Josephrp/Meteor-On-Mesh/firmwares/mayhem-firmware/hardware/portapack_h4m/CPLD_Schematic.pdf

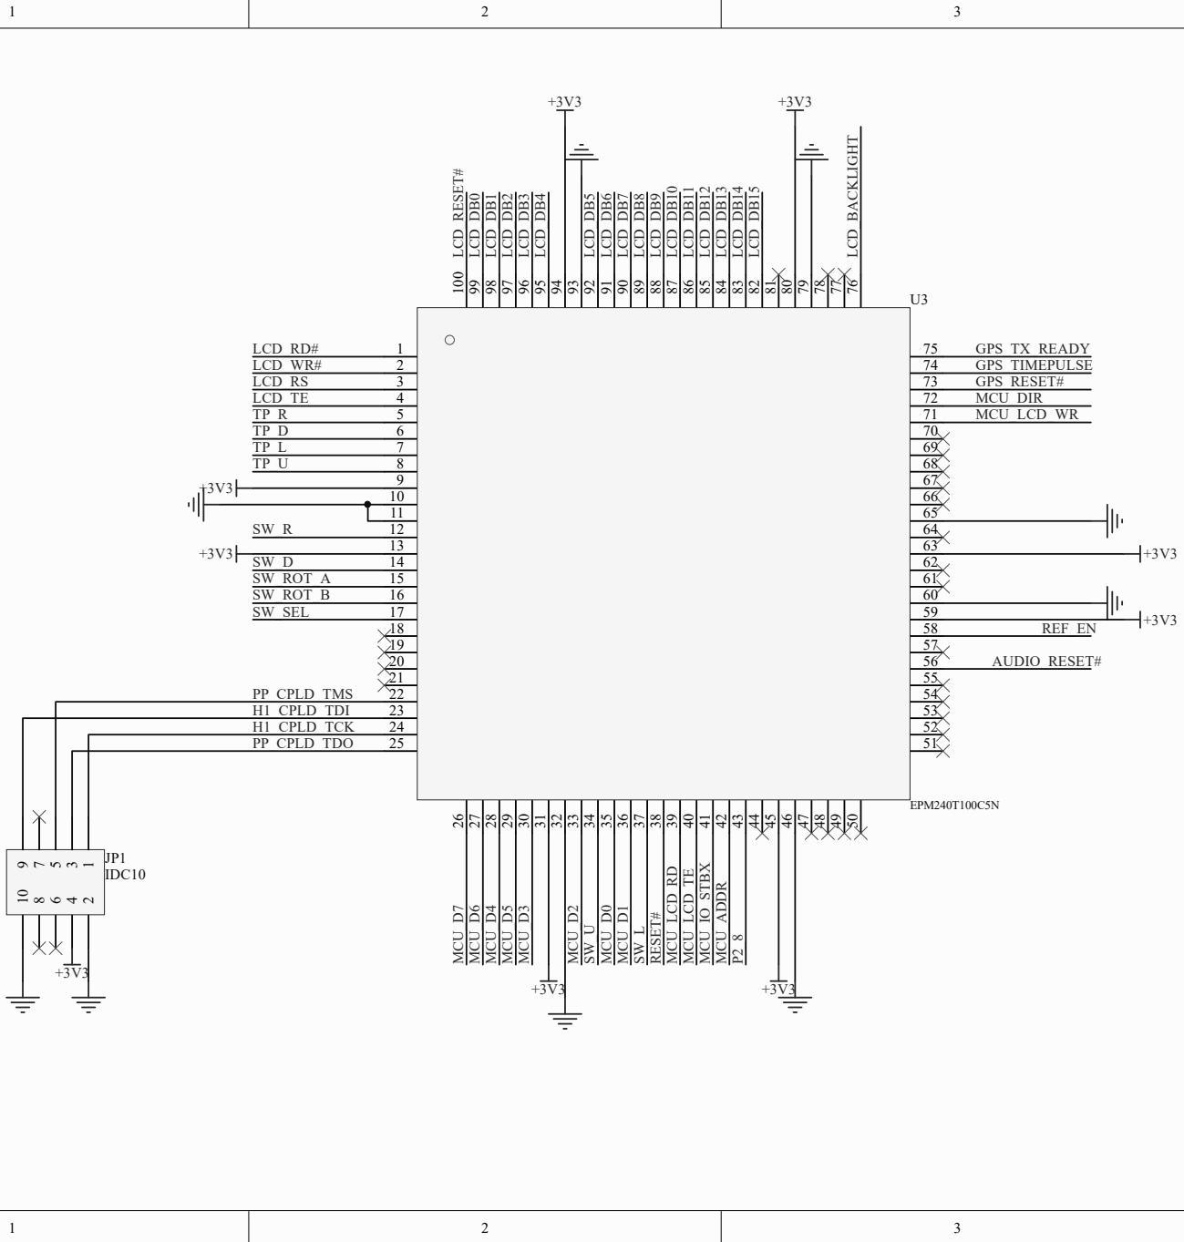
[picture p5: figure]
LCD_DB10; LCD_DB11; LCD_DB12; LCD_DB13; LCD_DB14; LCD_DB15; MCU_DIR MCU_LCD_WR; LCD_RESET#; LCD_BACKLIGHT; GPS_TX_READY GPS_TIMEPULSE; MCU_ADDR; PP_CPLD_TDO; MCU_D7; MCU_D6; MCU_D4; MCU_D5; MCU_D3; MCU_D2; MCU_D0; MCU_D1; RESET#; MCU_LCD_RD; MCU_LCD_TE; MCU_IO_STBX; H1_CPLD_TCK; SW_D SW_ROT_A SW_ROT_B SW_SEL; PP_CPLD_TMS H1_CPLD_TDI; GPS_RESET#; AUDIO_RESET#; REF_EN; LCD_TE; LCD_WR#; LCD_RD#; LCD_DB0; LCD_DB1; LCD_RS; LCD_DB2; LCD_DB3; LCD_DB4; LCD_DB5; LCD_DB6; LCD_DB7; LCD_DB8; LCD_DB9; EPM240T100C5N; JP1 IDC10

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
