Josephrp/Meteor-On-Mesh/firmwares/mayhem-firmware/docs/images/h2_cover.jpg

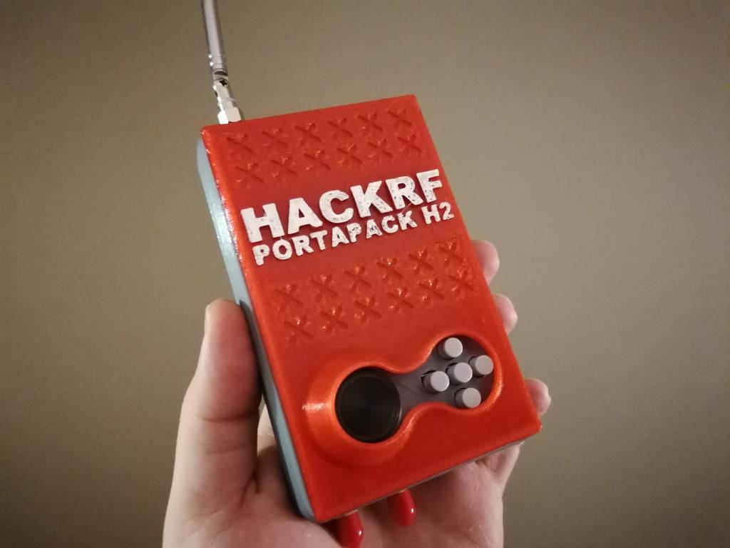
firmwares/mayhem-firmware/docs/images/h2_cover.jpg
