Josephrp/Meteor-On-Mesh/firmwares/mayhem-firmware/docs/images/h2_front.jpg

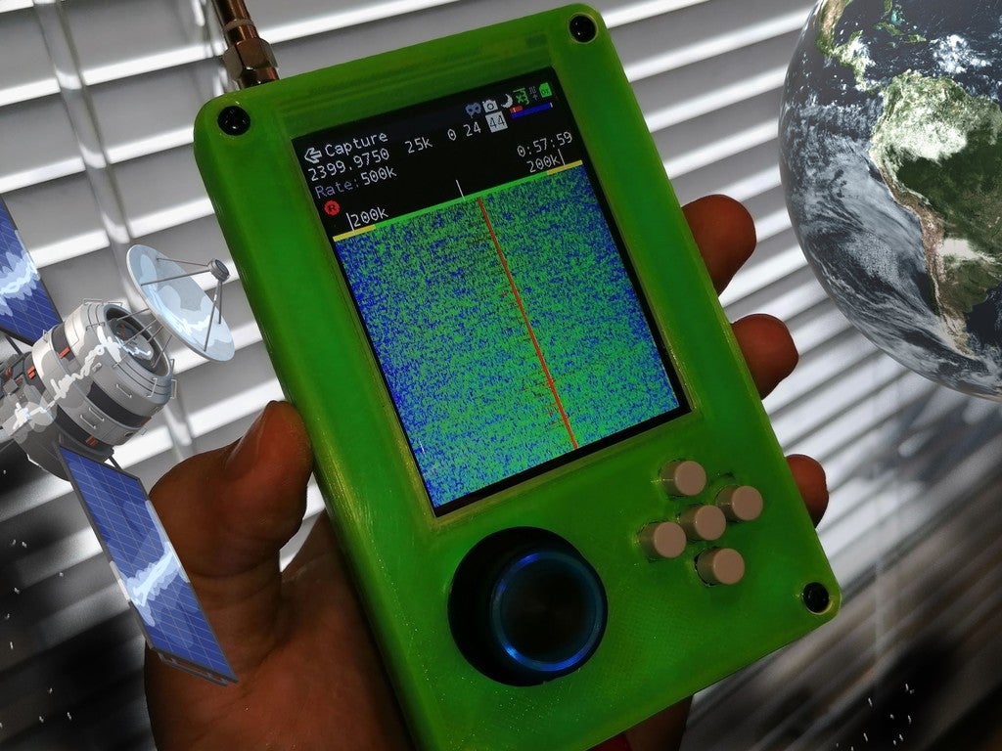
firmwares/mayhem-firmware/docs/images/h2_front.jpg
