Josephrp/Meteor-On-Mesh/firmwares/mayhem-firmware/firmware/chibios-portapack/ext/fatfs/doc/res/f7.png

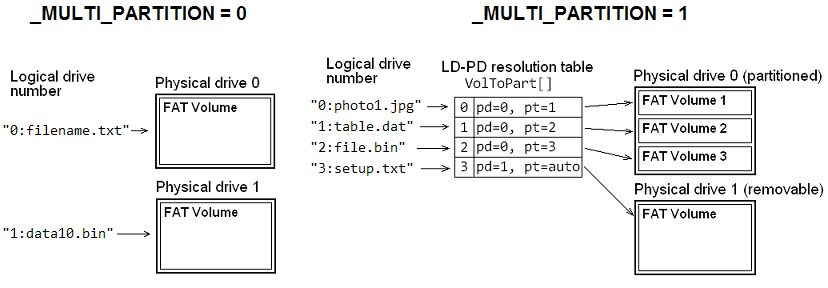
firmwares/mayhem-firmware/firmware/chibios-portapack/ext/fatfs/doc/res/f7.png
