Josephrp/Meteor-On-Mesh/firmwares/mayhem-firmware/firmware/chibios-portapack/ext/fatfs/doc/res/funcs.png

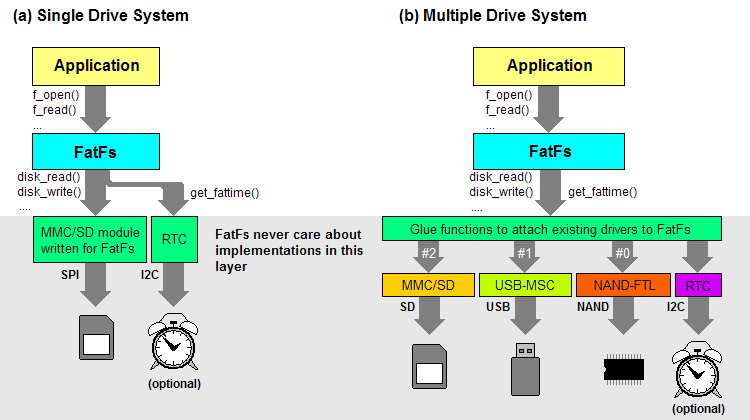
firmwares/mayhem-firmware/firmware/chibios-portapack/ext/fatfs/doc/res/funcs.png
