Josephrp/Meteor-On-Mesh/firmwares/mayhem-firmware/firmware/chibios-portapack/ext/fatfs/doc/res/modules.png

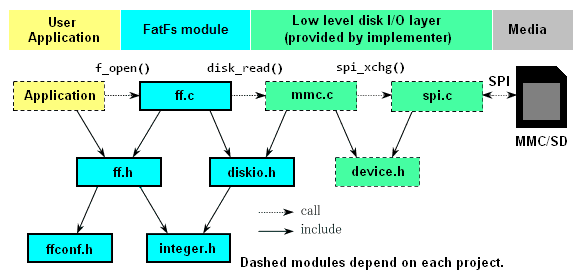
firmwares/mayhem-firmware/firmware/chibios-portapack/ext/fatfs/doc/res/modules.png
