Josephrp/Meteor-On-Mesh/firmwares/mayhem-firmware/hackrf/docs/images/block-diagram-pro.png

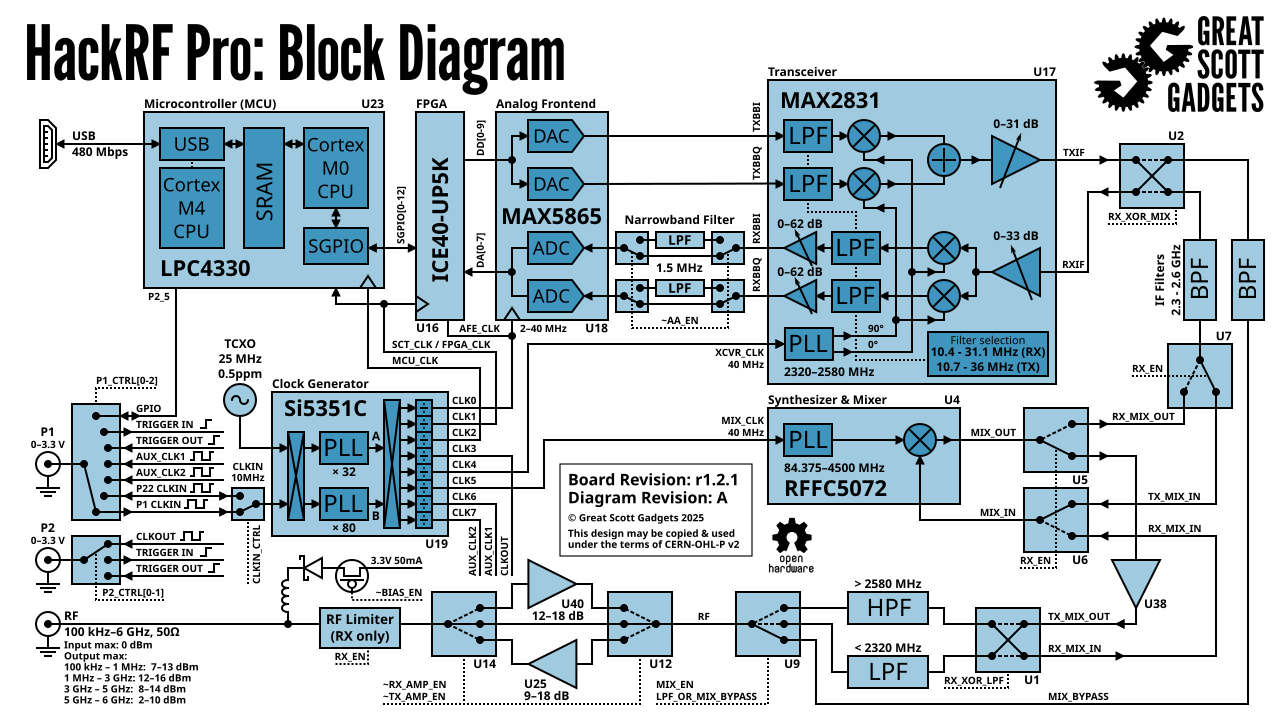
firmwares/mayhem-firmware/hackrf/docs/images/block-diagram-pro.png
