Josephrp/Meteor-On-Mesh/firmwares/mayhem-firmware/hackrf/docs/images/block-diagram-r9.png

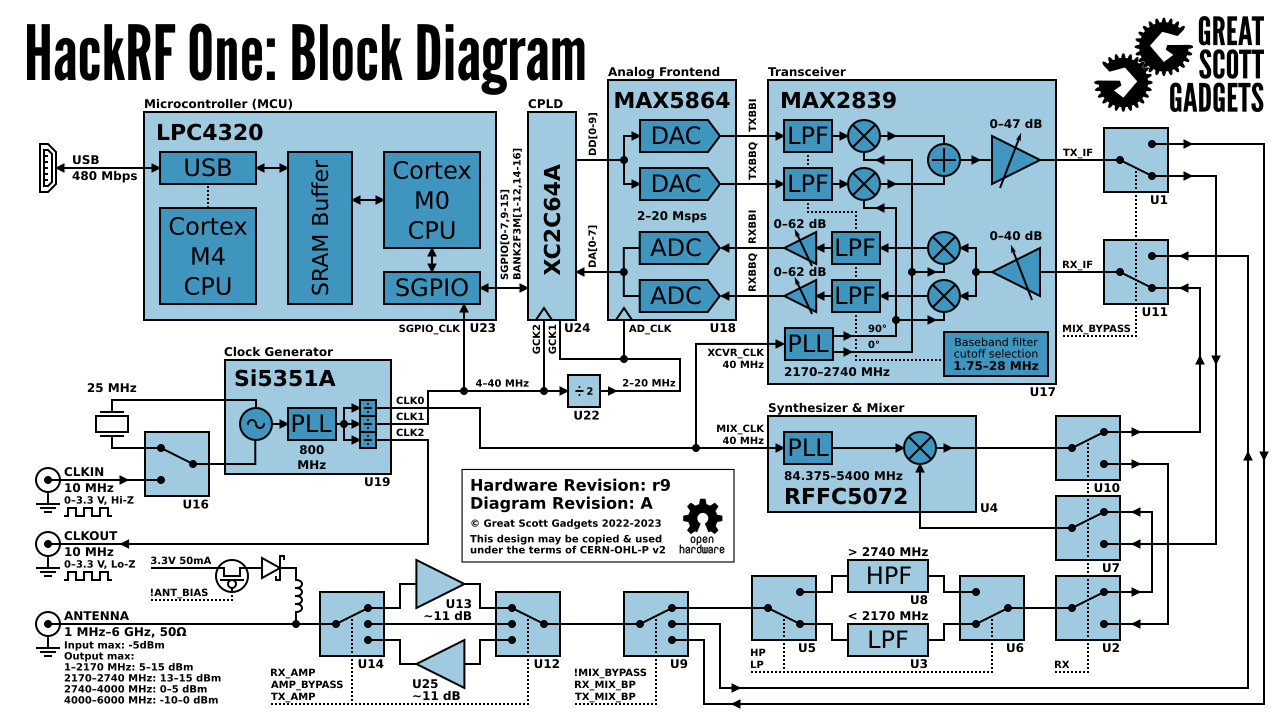
firmwares/mayhem-firmware/hackrf/docs/images/block-diagram-r9.png
