Josephrp/Meteor-On-Mesh/firmwares/mayhem-firmware/hackrf/docs/images/block-diagram.png

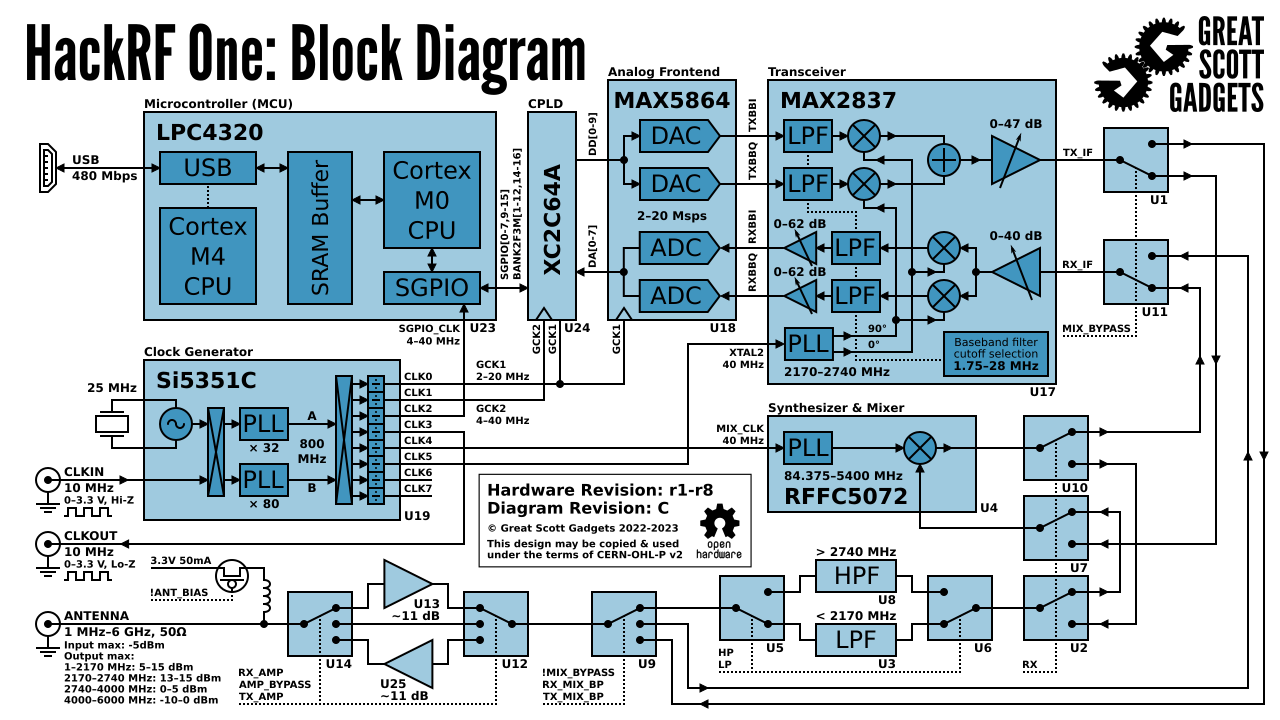
firmwares/mayhem-firmware/hackrf/docs/images/block-diagram.png
