Josephrp/Meteor-On-Mesh/firmwares/mayhem-firmware/hackrf/docs/images/dc_spike_example_plot.png

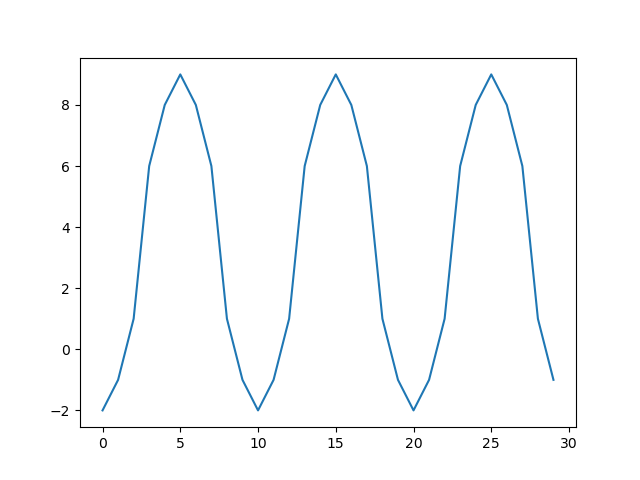
firmwares/mayhem-firmware/hackrf/docs/images/dc_spike_example_plot.png
