Josephrp/Meteor-On-Mesh/firmwares/mayhem-firmware/hackrf/docs/images/dc_spike_grc.png

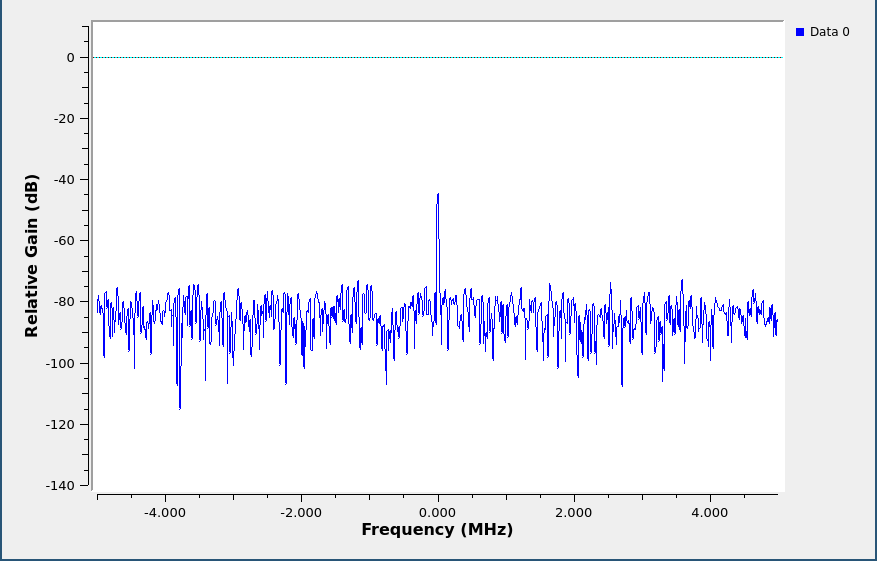
firmwares/mayhem-firmware/hackrf/docs/images/dc_spike_grc.png
