Josephrp/Meteor-On-Mesh/firmwares/mayhem-firmware/hackrf/docs/images/gateware-basic-block-diagram.png

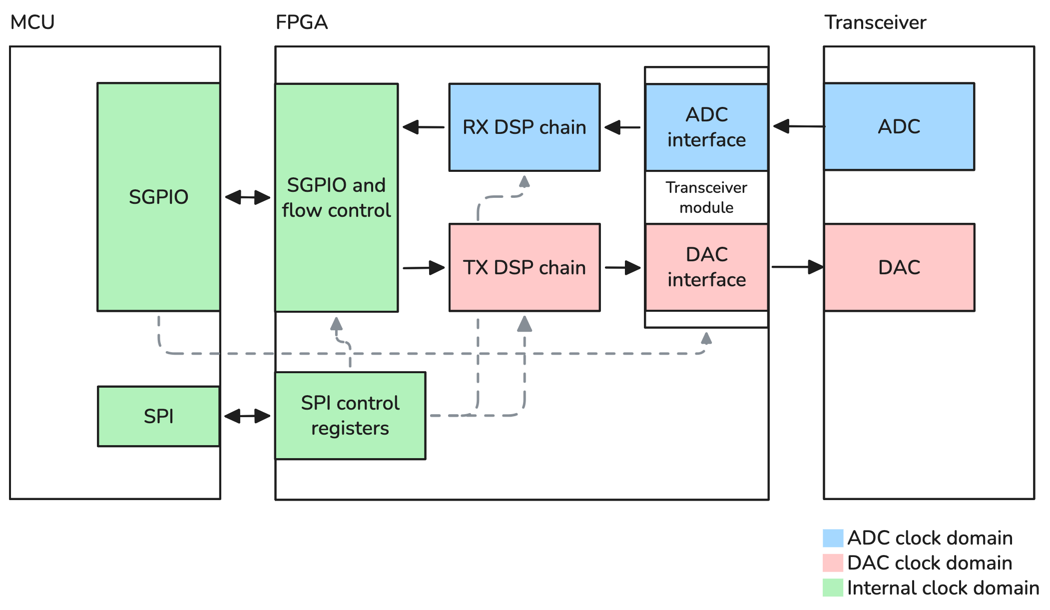
firmwares/mayhem-firmware/hackrf/docs/images/gateware-basic-block-diagram.png
