Josephrp/Meteor-On-Mesh/firmwares/mayhem-firmware/hackrf/docs/images/gateware-ext-prec-rx-dsp-chain.png

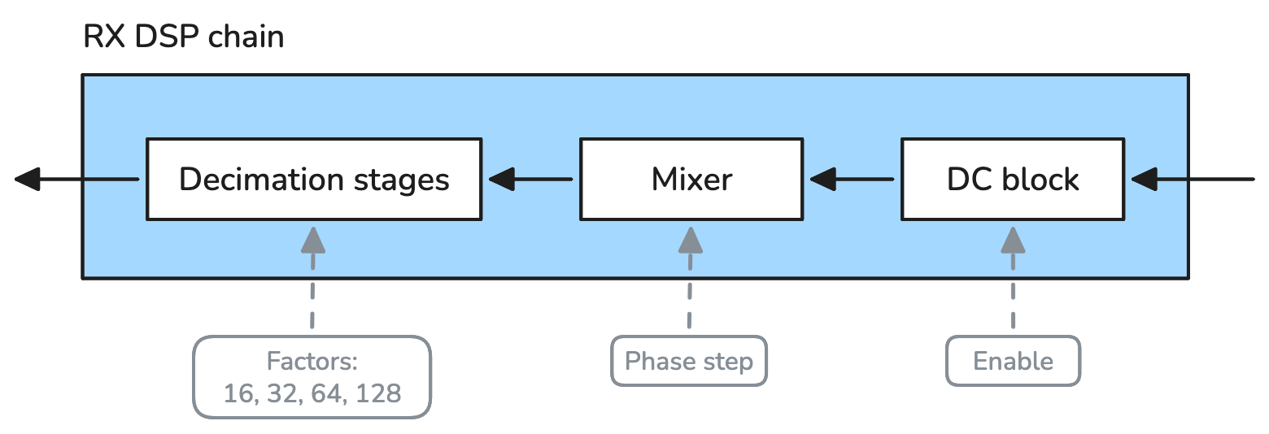
firmwares/mayhem-firmware/hackrf/docs/images/gateware-ext-prec-rx-dsp-chain.png
