Josephrp/Meteor-On-Mesh/firmwares/mayhem-firmware/hackrf/docs/images/gateware-ext-prec-tx-dsp-chain.png

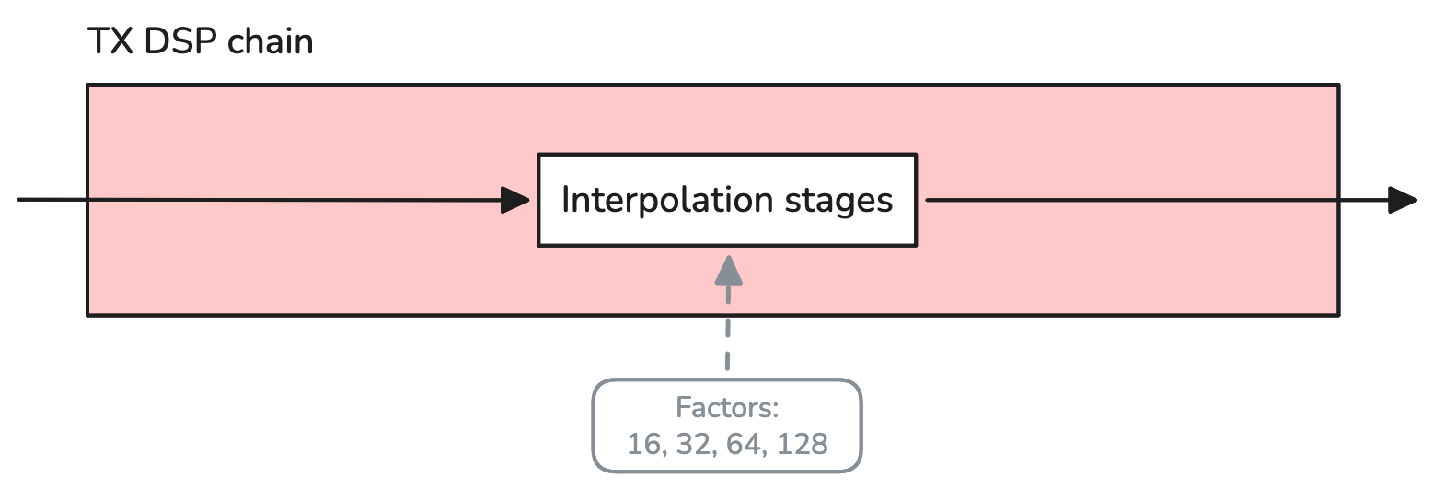
firmwares/mayhem-firmware/hackrf/docs/images/gateware-ext-prec-tx-dsp-chain.png
