Josephrp/Meteor-On-Mesh/firmwares/mayhem-firmware/hackrf/docs/images/gateware-halfprec-dsp-chain.png

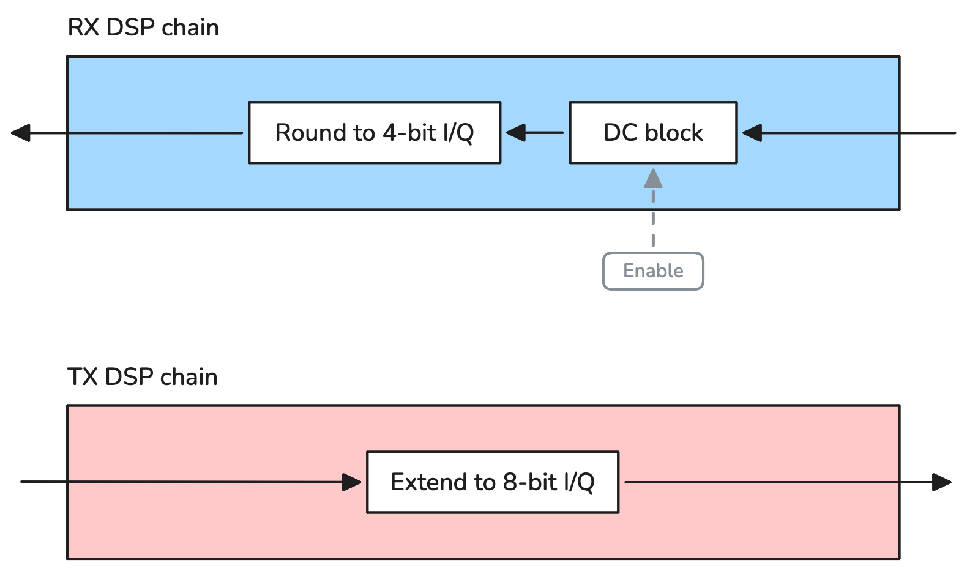
firmwares/mayhem-firmware/hackrf/docs/images/gateware-halfprec-dsp-chain.png
