Josephrp/Meteor-On-Mesh/firmwares/mayhem-firmware/hackrf/docs/images/gateware-rx-only-basic-block-diagram.png

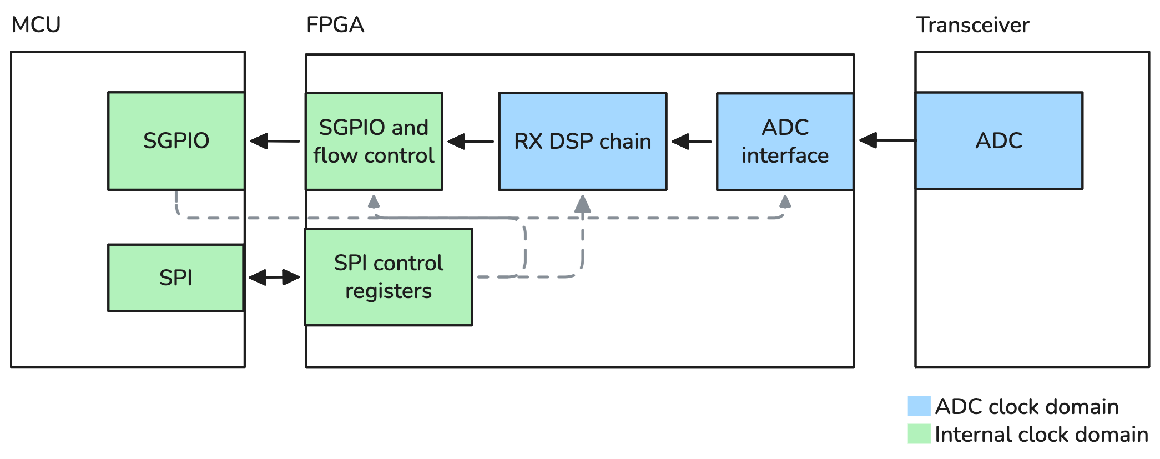
firmwares/mayhem-firmware/hackrf/docs/images/gateware-rx-only-basic-block-diagram.png
