Josephrp/Meteor-On-Mesh/firmwares/mayhem-firmware/hackrf/docs/images/gateware-standard-dsp-chain.png

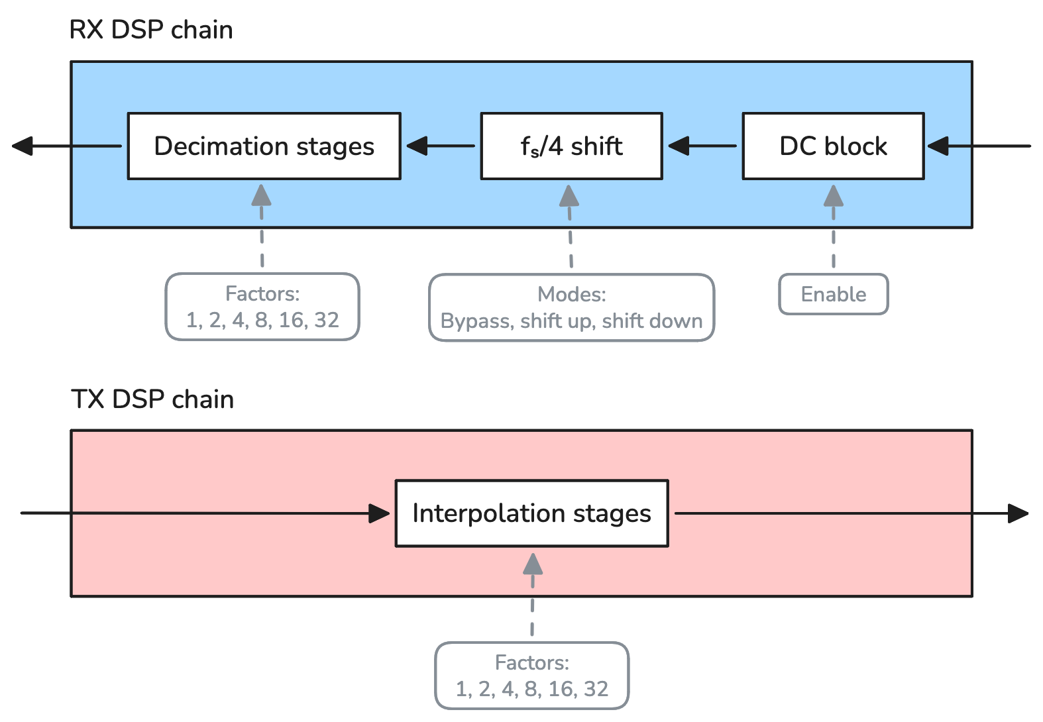
firmwares/mayhem-firmware/hackrf/docs/images/gateware-standard-dsp-chain.png
