Josephrp/Meteor-On-Mesh/firmwares/mayhem-firmware/hackrf/docs/images/grc-hw-sync-streaming.png

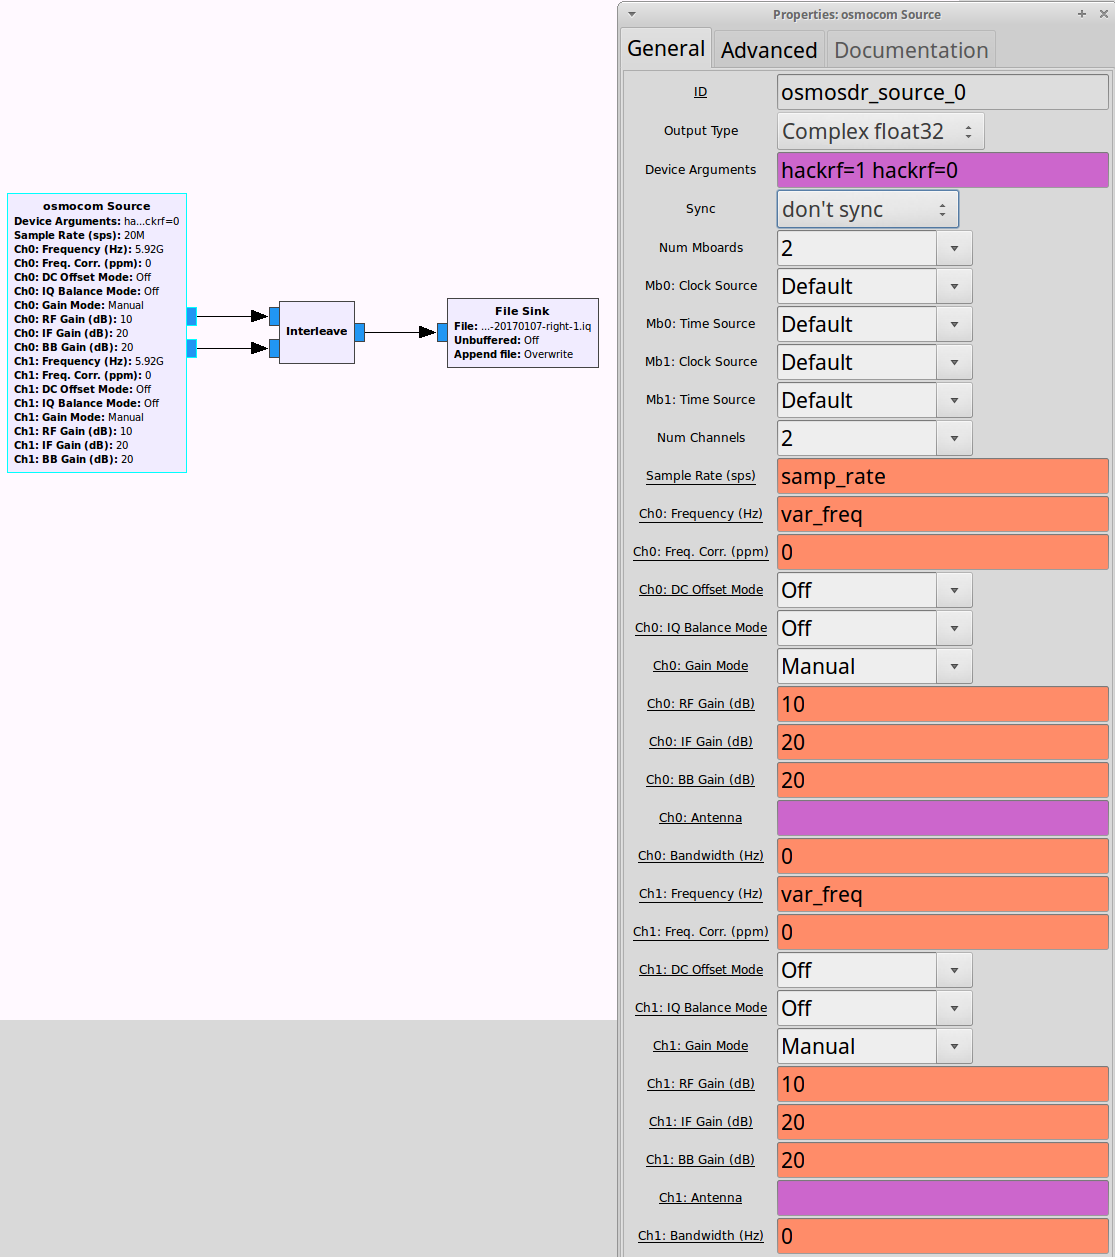
firmwares/mayhem-firmware/hackrf/docs/images/grc-hw-sync-streaming.png
