Josephrp/Meteor-On-Mesh/firmwares/mayhem-firmware/hackrf/docs/images/hackrf-pro-preliminary-photo.jpg

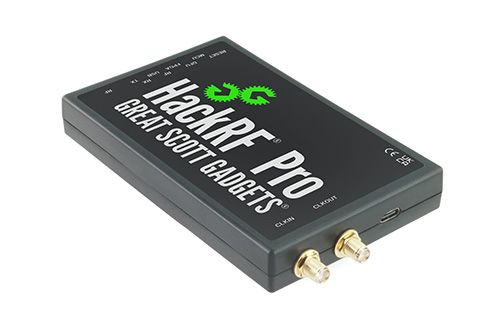
firmwares/mayhem-firmware/hackrf/docs/images/hackrf-pro-preliminary-photo.jpg
