Josephrp/Meteor-On-Mesh/firmwares/mayhem-firmware/hackrf/docs/images/jawbreaker.JPG

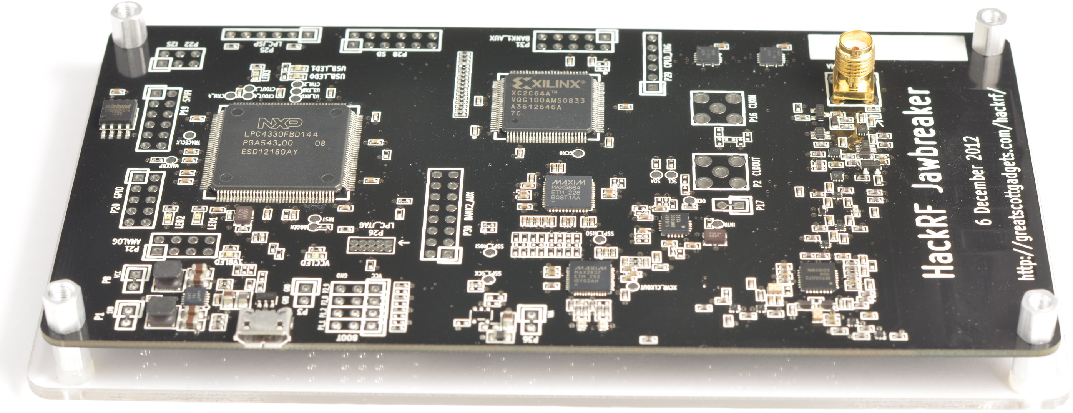
firmwares/mayhem-firmware/hackrf/docs/images/jawbreaker.JPG
