Josephrp/Meteor-On-Mesh/firmwares/mayhem-firmware/hackrf/docs/images/noisereducingcable.jpeg

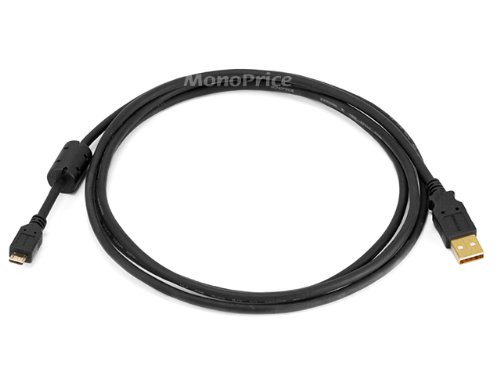
firmwares/mayhem-firmware/hackrf/docs/images/noisereducingcable.jpeg
