Josephrp/Meteor-On-Mesh/firmwares/mayhem-firmware/hackrf/docs/images/noisereducingcablescreenshot.jpeg

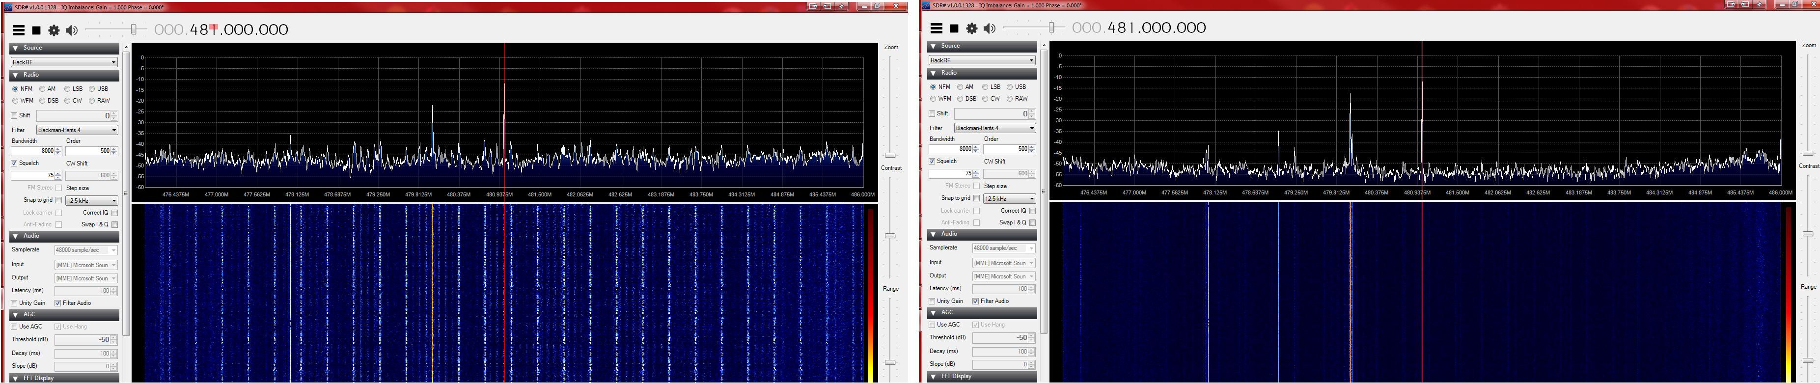
firmwares/mayhem-firmware/hackrf/docs/images/noisereducingcablescreenshot.jpeg
