Josephrp/Meteor-On-Mesh/firmwares/mayhem-firmware/hackrf/docs/images/operacake-block-diagram.png

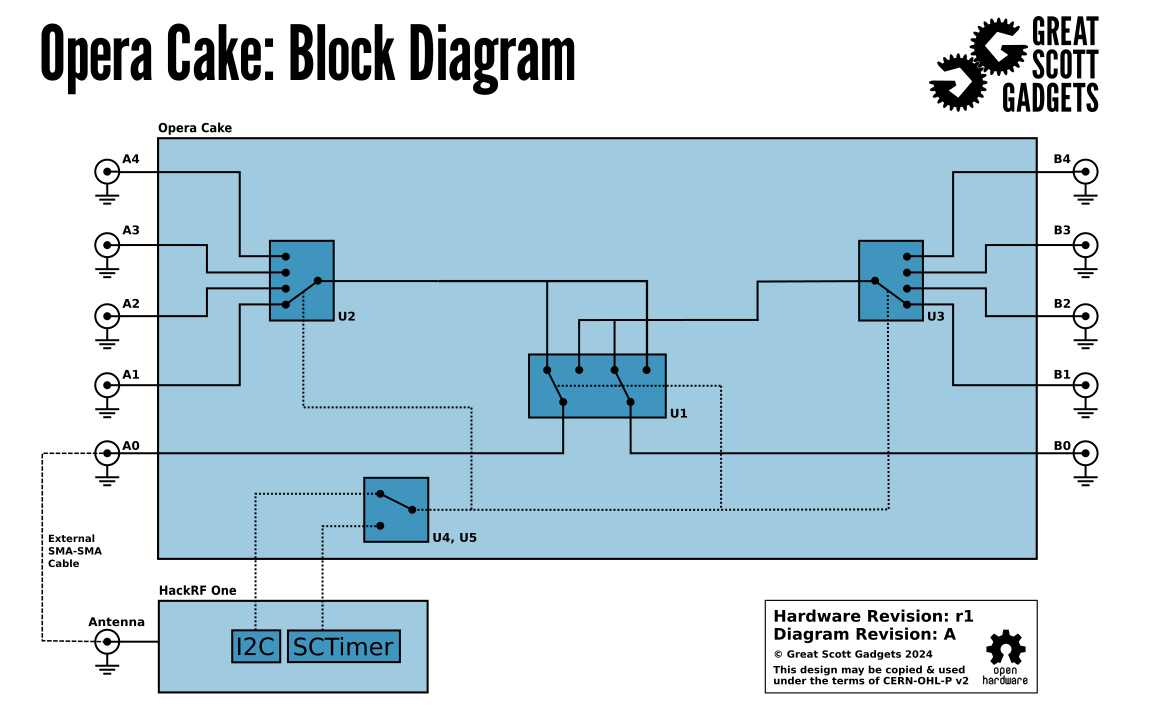
firmwares/mayhem-firmware/hackrf/docs/images/operacake-block-diagram.png
