Josephrp/Meteor-On-Mesh/firmwares/mayhem-firmware/hackrf/docs/images/operacake.jpeg

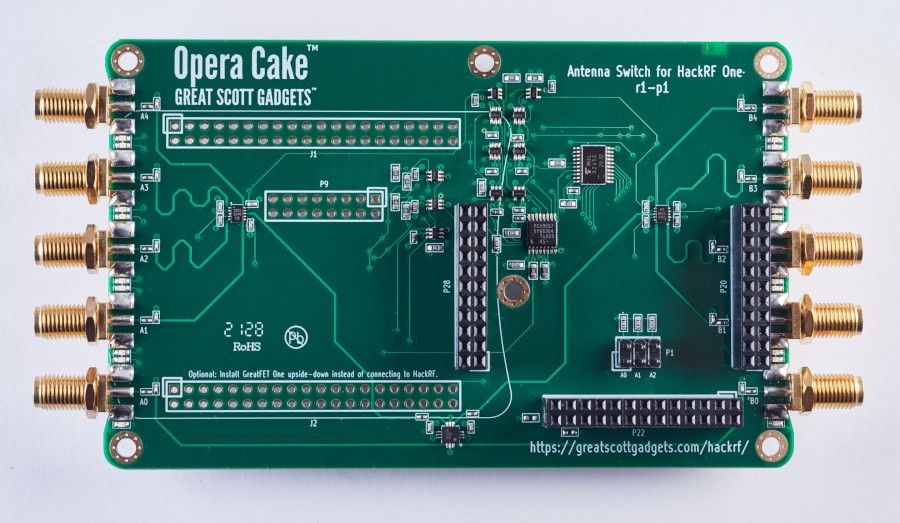
firmwares/mayhem-firmware/hackrf/docs/images/operacake.jpeg
