Josephrp/Meteor-On-Mesh/firmwares/mayhem-firmware/hackrf/docs/images/rad1o_8.jpg

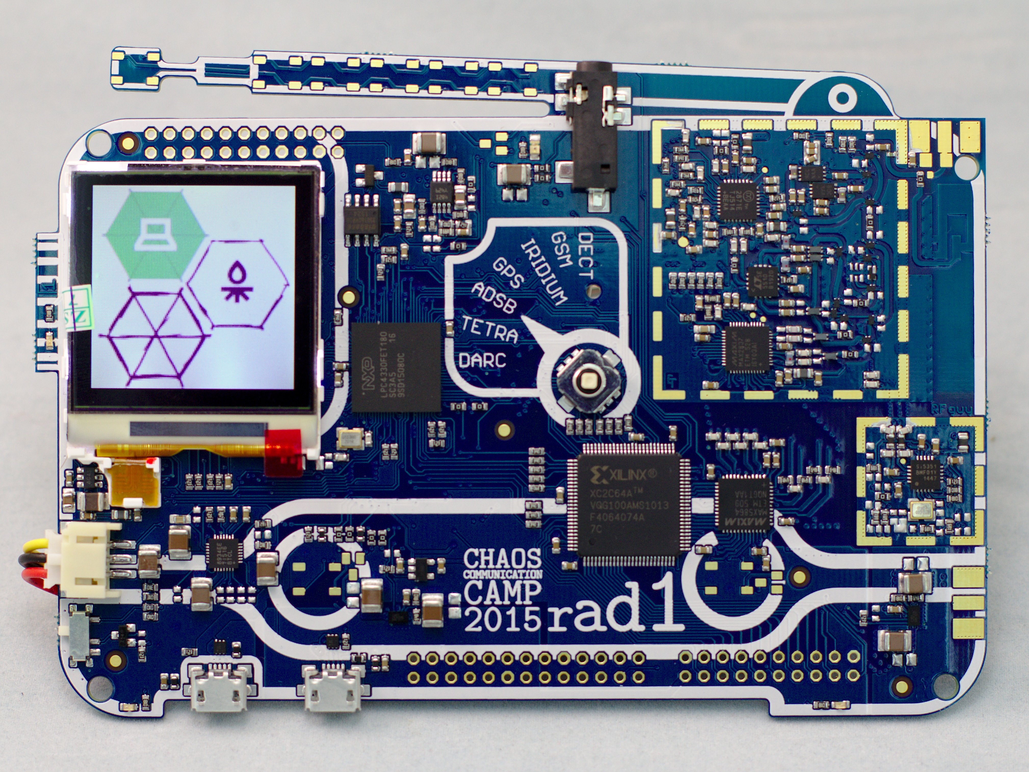
firmwares/mayhem-firmware/hackrf/docs/images/rad1o_8.jpg
