Josephrp/Meteor-On-Mesh/firmwares/mayhem-firmware/hackrf/docs/images/rf_shield_6.jpg

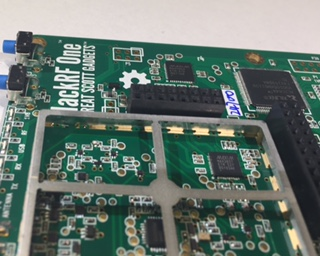
firmwares/mayhem-firmware/hackrf/docs/images/rf_shield_6.jpg
