Josephrp/Meteor-On-Mesh/firmwares/mayhem-firmware/hackrf/docs/images/trigger-pins.png

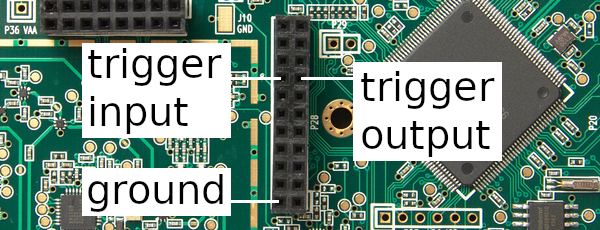
firmwares/mayhem-firmware/hackrf/docs/images/trigger-pins.png
