Josephrp/Meteor-On-Mesh/firmwares/mayhem-firmware/sdcard/SAMPLES/LED/Aurora_RGB/remote.jpeg

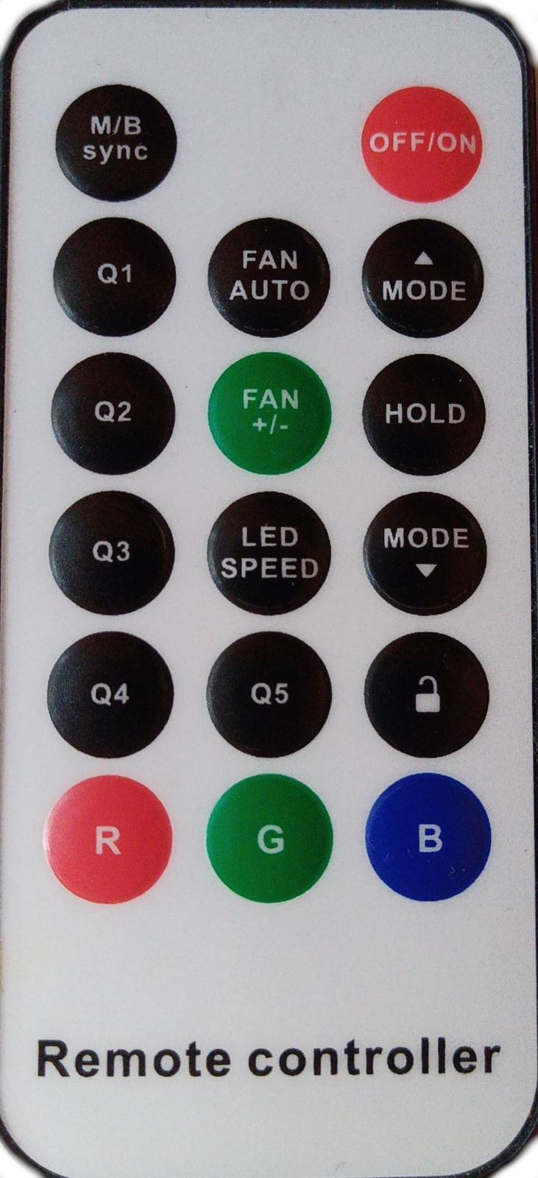
firmwares/mayhem-firmware/sdcard/SAMPLES/LED/Aurora_RGB/remote.jpeg
