Josephrp/Meteor-On-Mesh/firmwares/mayhem-firmware/sdcard/SSTV/320240BW.bmp

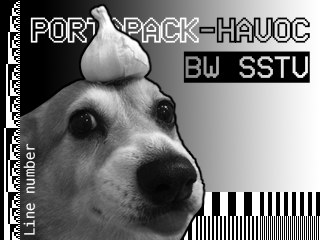
firmwares/mayhem-firmware/sdcard/SSTV/320240BW.bmp
