Josephrp/Meteor-On-Mesh/firmwares/mayhem-firmware/sdcard/SSTV/320256C.bmp

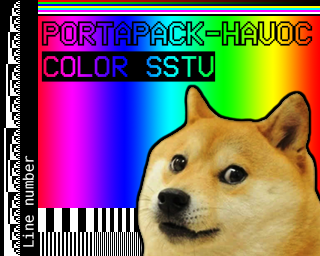
firmwares/mayhem-firmware/sdcard/SSTV/320256C.bmp
