Josephrp/Meteor-On-Mesh/firmwares/mayhem-firmware/sdcard/SSTV/sstvtest.bmp

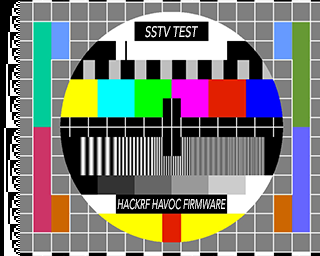
firmwares/mayhem-firmware/sdcard/SSTV/sstvtest.bmp
