Josephrp/Meteor-On-Mesh/firmwares/mayhem-mdk/ScreenShots/ADSB_mycoords.png

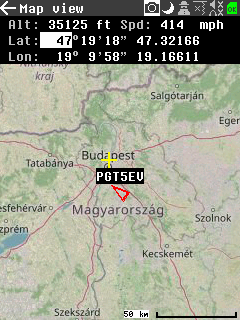
firmwares/mayhem-mdk/ScreenShots/ADSB_mycoords.png
