Josephrp/Meteor-On-Mesh/firmwares/mayhem-mdk/ScreenShots/ADSB_mycoords_with_orientation.png

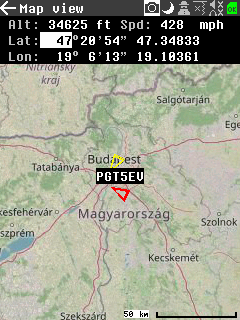
firmwares/mayhem-mdk/ScreenShots/ADSB_mycoords_with_orientation.png
