Josephrp/Meteor-On-Mesh/firmwares/mayhem-mdk/ScreenShots/esp32pp_web.png

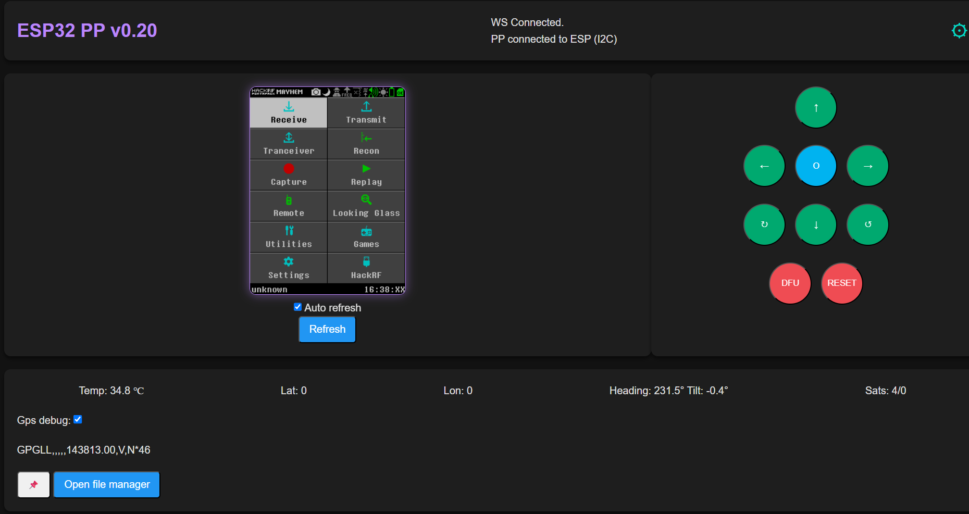
firmwares/mayhem-mdk/ScreenShots/esp32pp_web.png
