Josephrp/Meteor-On-Mesh/firmwares/mayhem-mdk/ScreenShots/flash.png

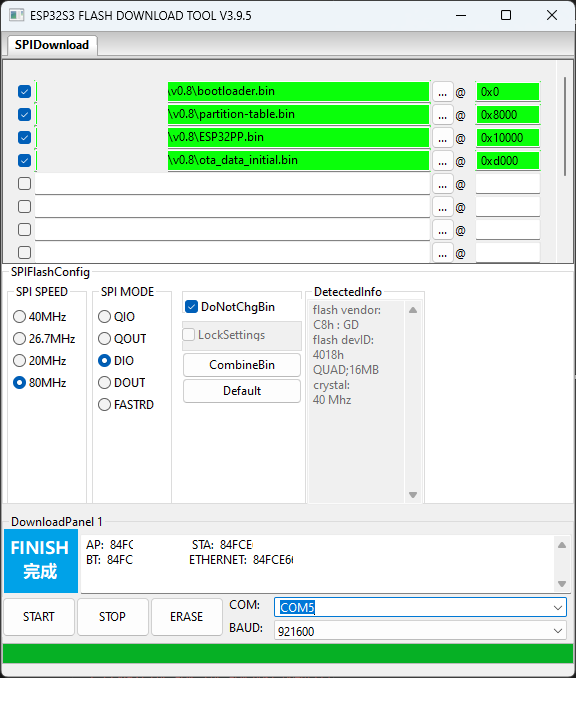
firmwares/mayhem-mdk/ScreenShots/flash.png
