Josephrp/Meteor-On-Mesh/firmwares/mayhem-mdk/ScreenShots/foxhunt.png

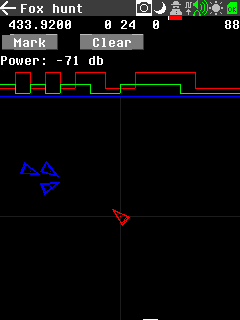
firmwares/mayhem-mdk/ScreenShots/foxhunt.png
