Josephrp/Meteor-On-Mesh/firmwares/mayhem-mdk/ScreenShots/sattrack.png

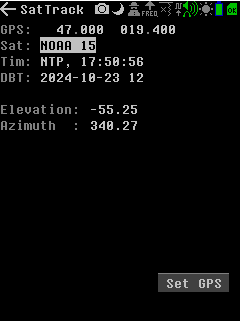
firmwares/mayhem-mdk/ScreenShots/sattrack.png
