Josephrp/Meteor-On-Mesh/firmwares/meshtastic/src/graphics/niche/InkHUD/docs/appletfont.png

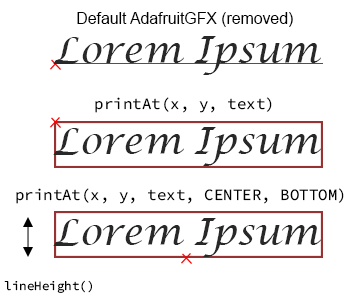
firmwares/meshtastic/src/graphics/niche/InkHUD/docs/appletfont.png
