Josephrp/Meteor-On-Mesh/firmwares/meshtastic/src/graphics/niche/InkHUD/docs/disclaimer.jpg

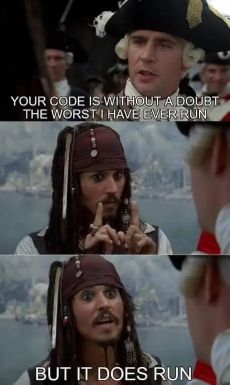
firmwares/meshtastic/src/graphics/niche/InkHUD/docs/disclaimer.jpg
