Josephrp/Meteor-On-Mesh/firmwares/meshtastic/src/graphics/niche/InkHUD/docs/rendering.gif

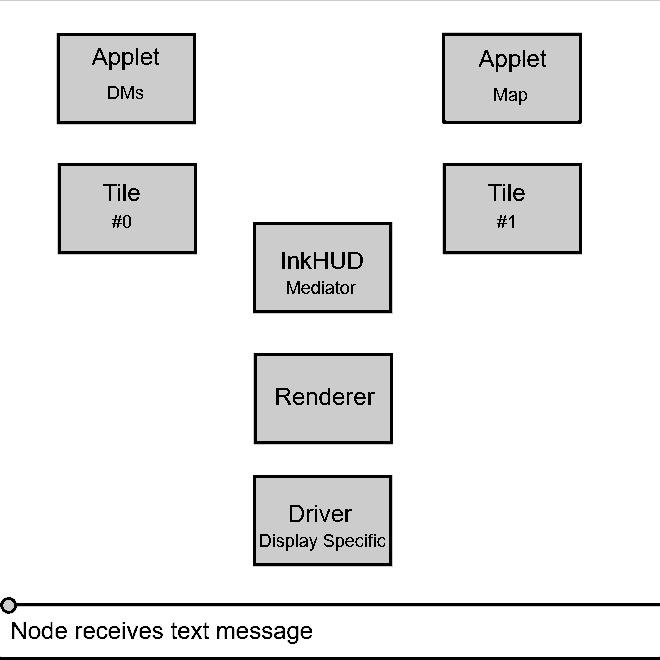
firmwares/meshtastic/src/graphics/niche/InkHUD/docs/rendering.gif
