Josephrp/Meteor-On-Mesh/firmwares/meshtastic/src/graphics/niche/InkHUD/docs/tile_translation.png

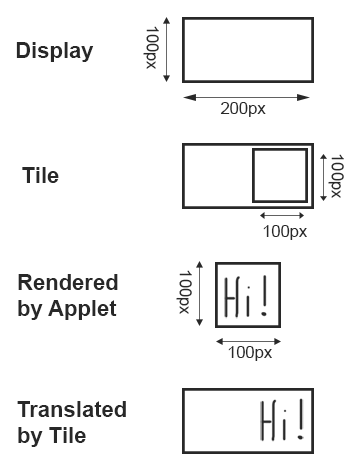
firmwares/meshtastic/src/graphics/niche/InkHUD/docs/tile_translation.png
