Josephrp/Meteor-On-Mesh/firmwares/meshtastic/variants/nrf52840/diy/nrf52_promicro_diy_tcxo/E80_RSSI_per_case.webp

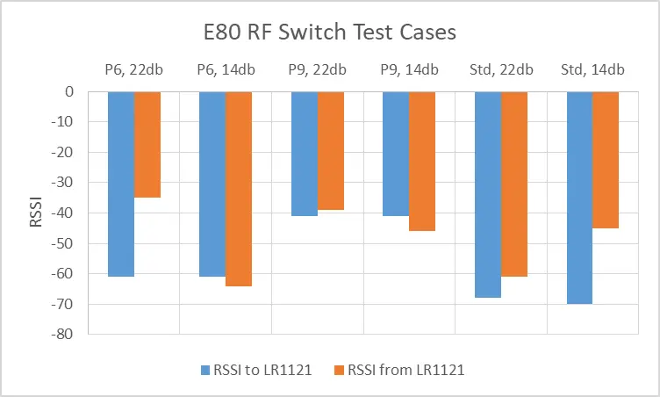
firmwares/meshtastic/variants/nrf52840/diy/nrf52_promicro_diy_tcxo/E80_RSSI_per_case.webp
