Josephrp/Meteor-On-Mesh/static/IMG_20260624_184421.jpg

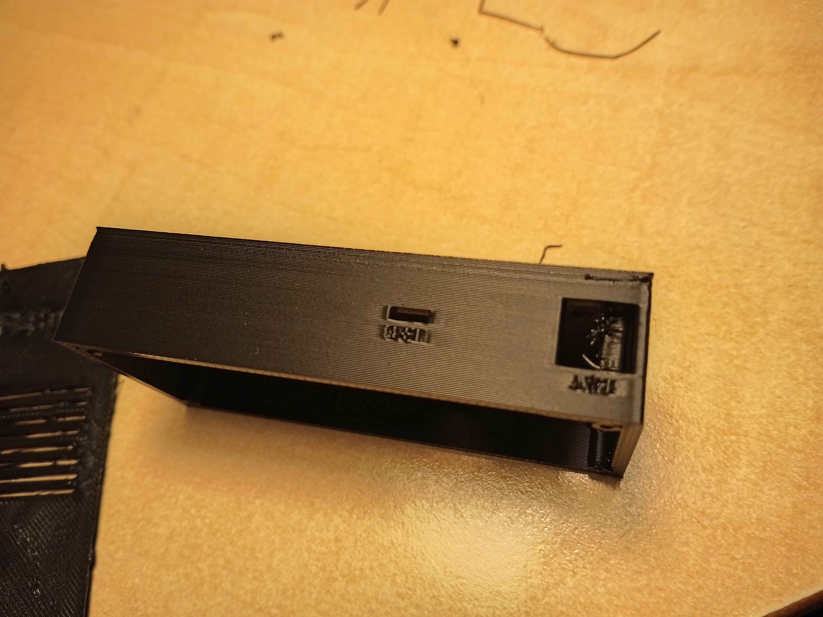
static/IMG_20260624_184421.jpg
