Josephrp/Meteor-On-Mesh/firmwares/mayhem-firmware/hardware/portapack_h4m/3d_printed/README.md

Upgraded standard case<br>https://www.printables.com/model/1337429-upgraded-hackrf-portapack-h4h4m-case

Upgraded 18650 version case<br>https://www.printables.com/model/1337451-18650-power-hackrf-portapack-h4m-case

Official case, made for injection molding. Can be 3D printed, but has very tight tolerances.<br>https://www.printables.com/model/1019145-official-hackrf-portapack-h4h4m-case/comments
