Josephrp/Meteor-On-Mesh/firmwares/mayhem-mdk/ScreenShots/esp32pp_example_assembly.png

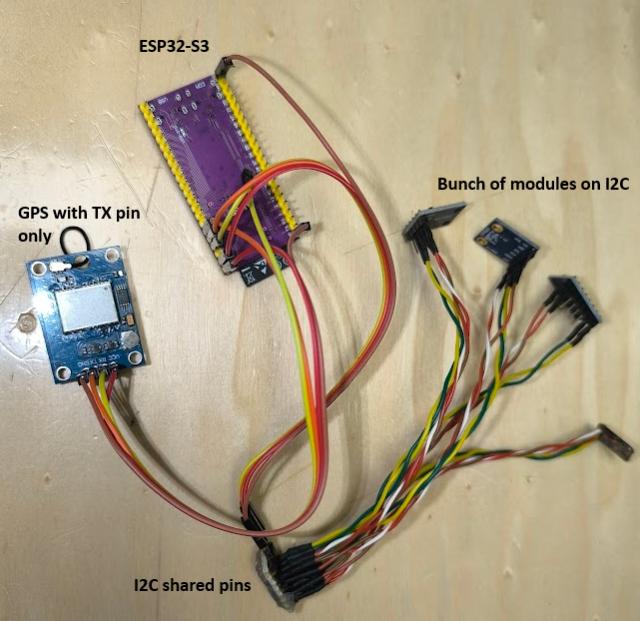
firmwares/mayhem-mdk/ScreenShots/esp32pp_example_assembly.png
