Josephrp/Meteor-On-Mesh/firmwares/mayhem-mdk/ScreenShots/ExtSensorTester.png

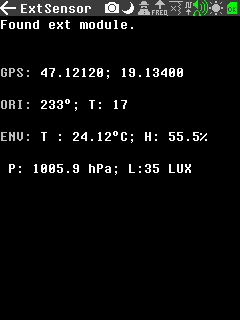
firmwares/mayhem-mdk/ScreenShots/ExtSensorTester.png
