Josephrp/Meteor-On-Mesh/firmwares/mayhem-firmware/hardware/portapack_h1/portapack_h1.pdf

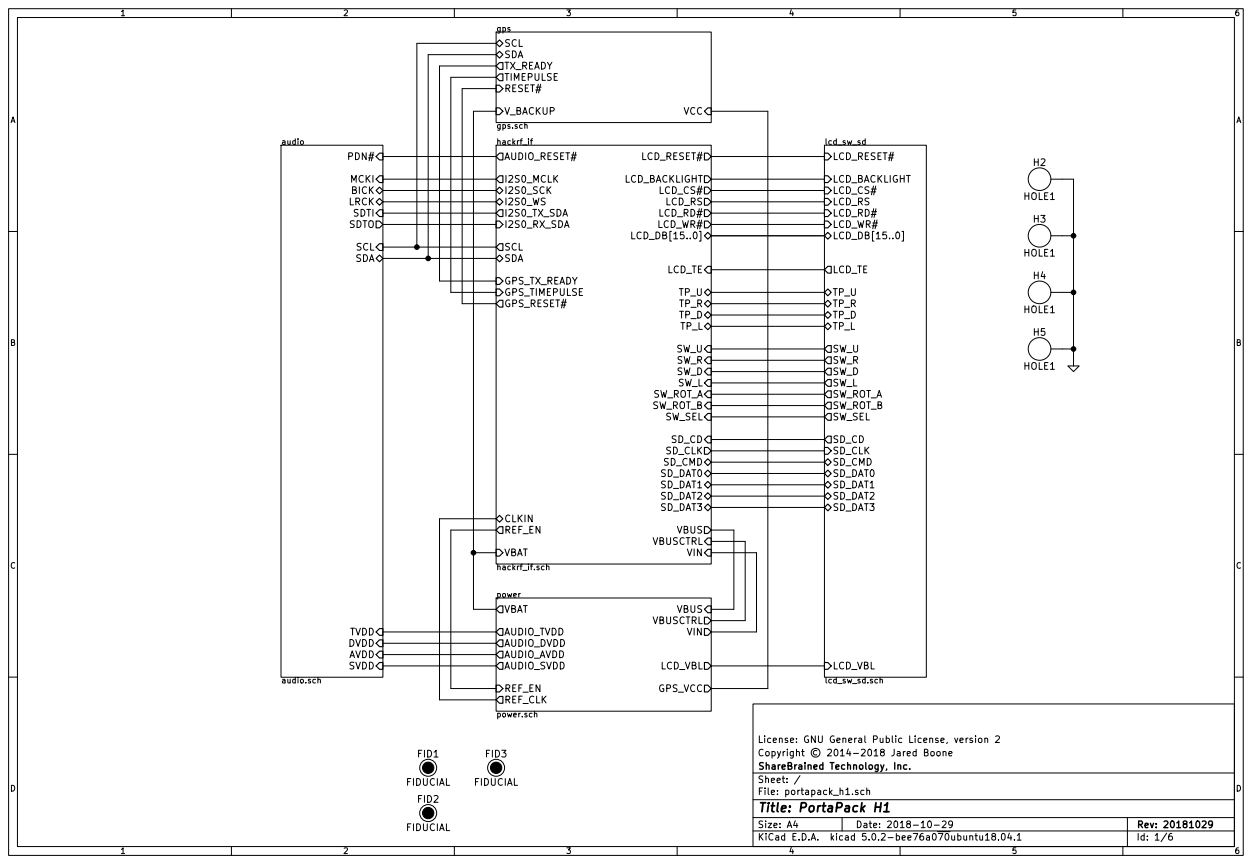
[picture p82: page 1]

License: GNU General Public License, version 2
Copyright © 2014-2018 Jared Boone
File: portapack_h1.sch Sheet: / ShareBrained Technology, Inc.

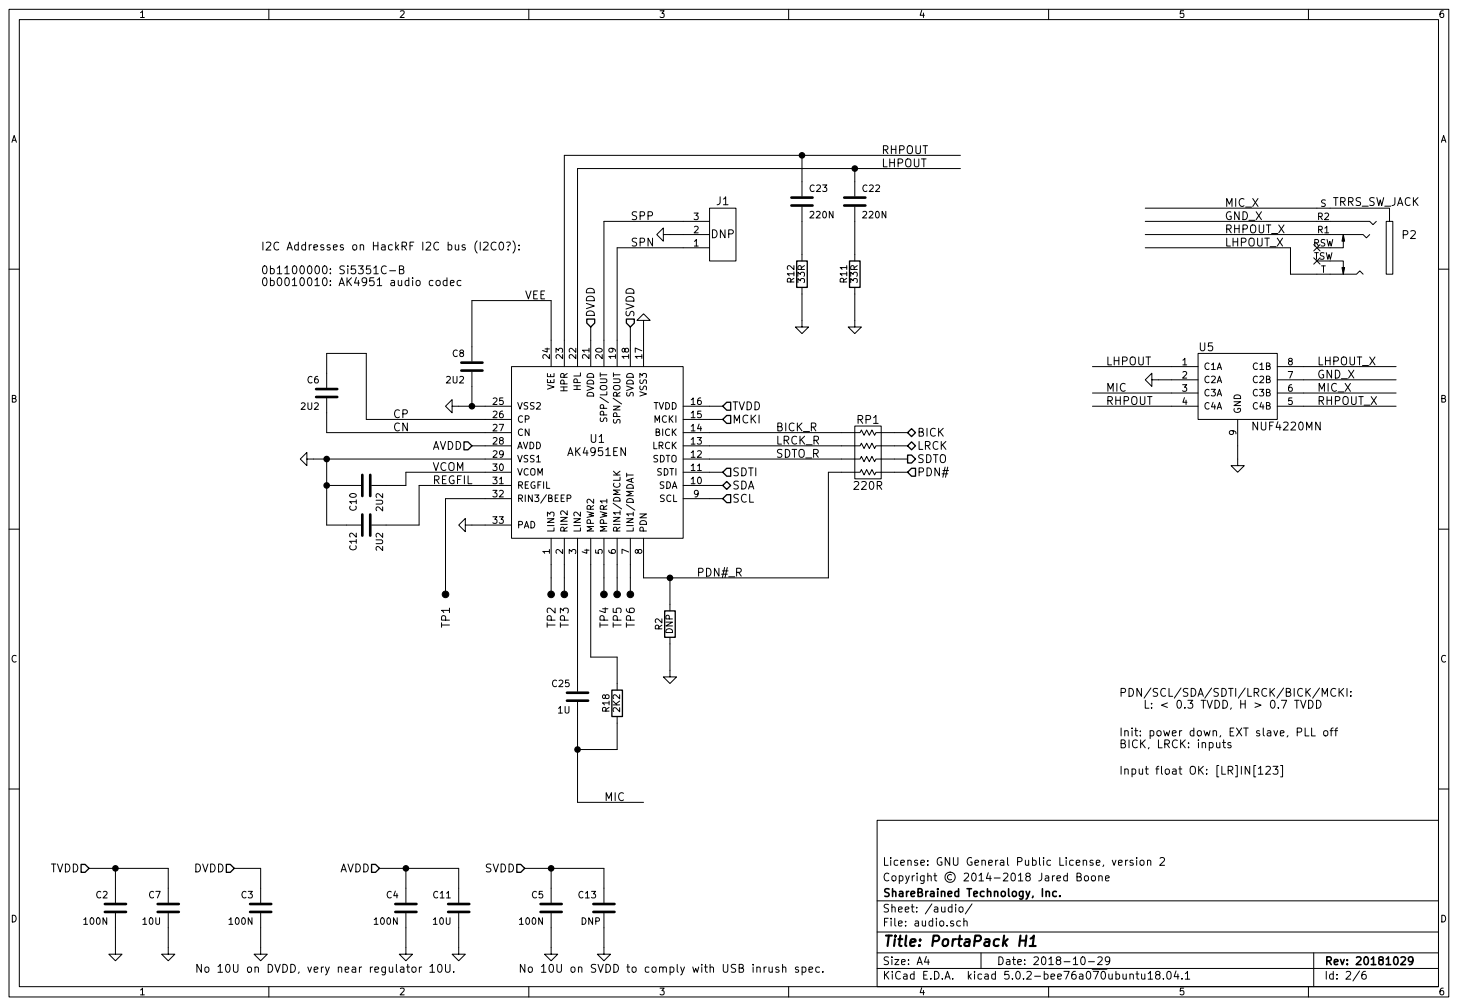
[picture p83: page 2]

I2C Addresses on HackRF I2C bus (I2C0?):

8 SCL 9 SDA 10 SPP/LOUT 20 VCOM 30 SDTI 11 DVDD 21 REGFIL 31 SDTO 12 HPL 22 RIN3/BEEP 32

LRCK_R
SDTO_R

PDN/SCL/SDA/SDTI/LRCK/BICK/MCKI:
L: < 0.3 TVDD, H > 0.7 TVDD

Init: power down, EXT slave, PLL off
BICK, LRCK: inputs

Copyright © 2014-2018 Jared Boone
File: audio.sch Sheet: /audio/ ShareBrained Technology, Inc.

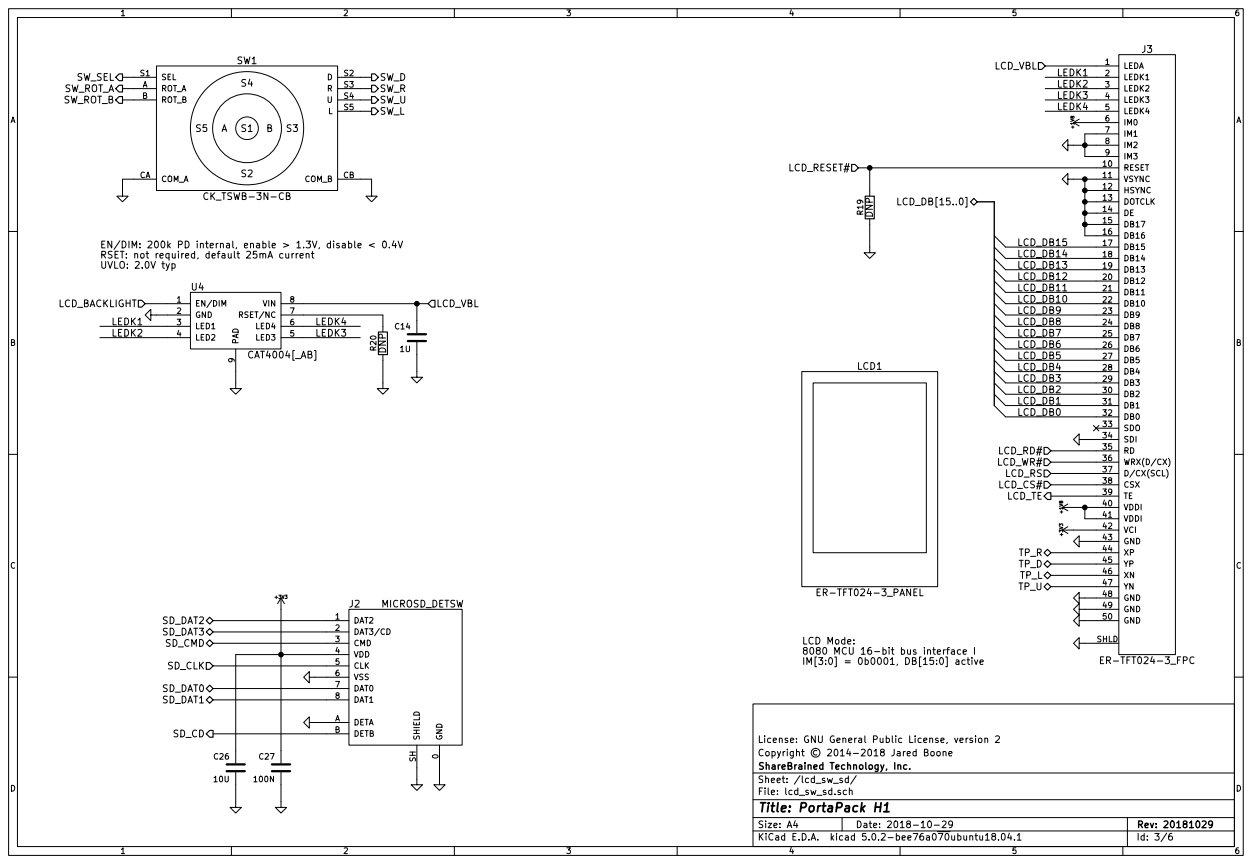
[picture p84: page 3]

EN/DIM: 200k PD internal, enable > 1.3V, disable < 0.4V
RSET: not required, default 25mA current
UVLO: 2.0V typ

LCD Mode:
8080 MCU 16-bit bus interface I
IM[3:0] = 0b0001, DB[15:0] active

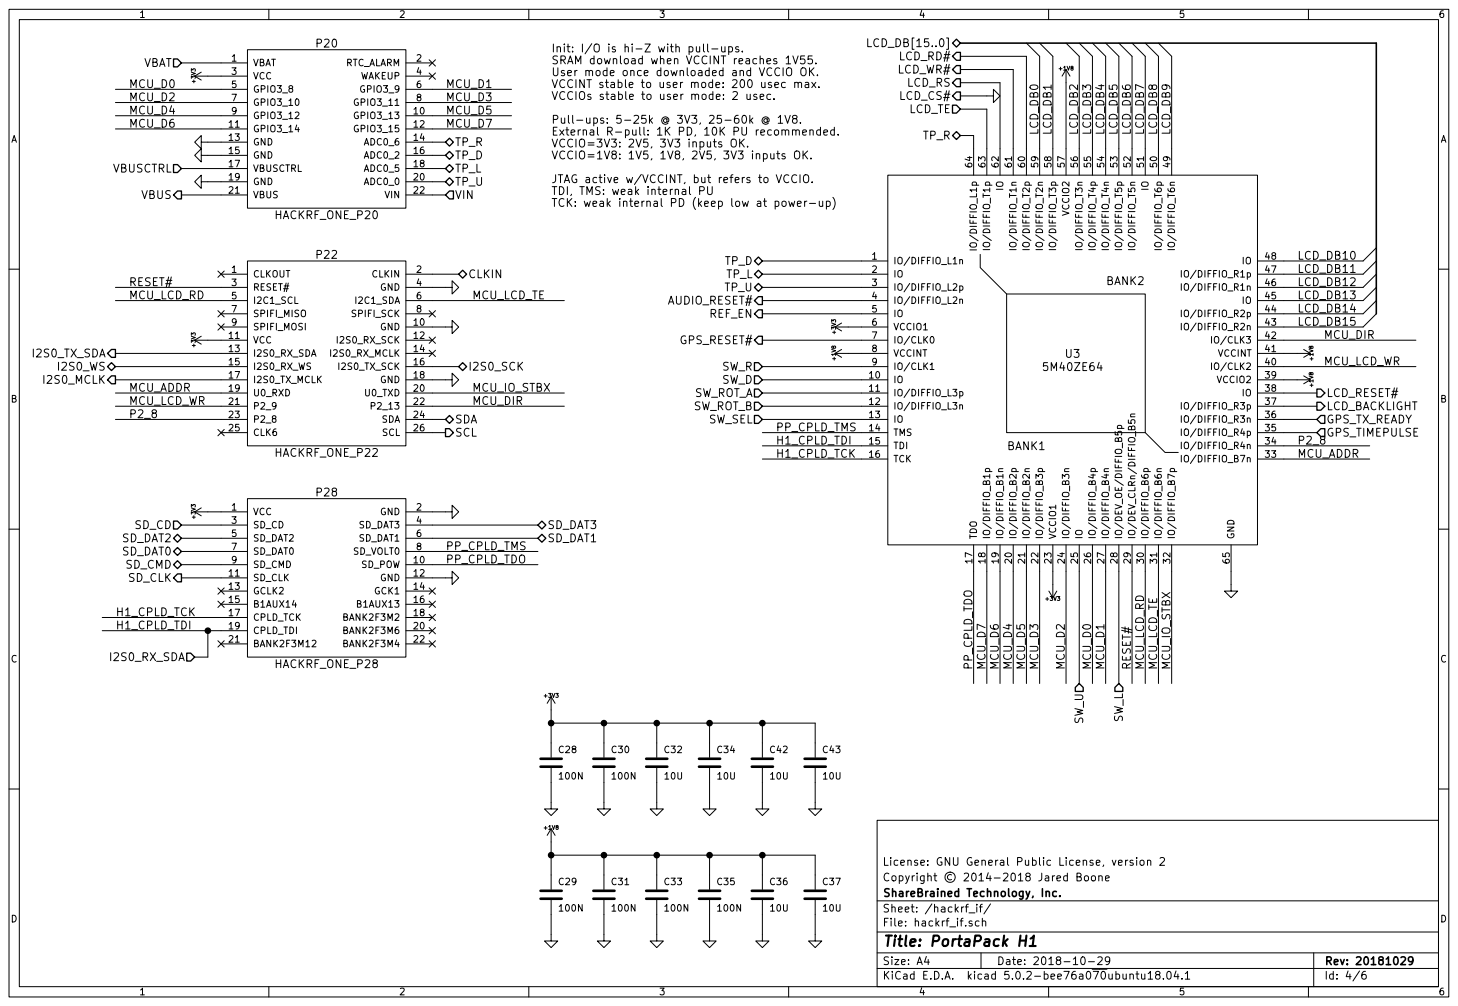
[picture p85: page 4]

Init: I/O is hi-Z with pull-ups.
SRAM download when VCCINT reaches 1V55.
User mode once downloaded and VCCIO OK.
VCCINT stable to user mode: 200 usec max.
VCCIOs stable to user mode: 2 usec.
Pull-ups: 5-25k @ 3V3, 25-60k @ 1V8.
External R-pull: 1K PD, 10K PU recommended.
VCCIO=3V3: 2V5, 3V3 inputs OK.
VCCIO=1V8: 1V5, 1V8, 2V5, 3V3 inputs OK.
JTAG active w/VCCINT, but refers to VCCIO.
TDI, TMS: weak internal PU
TCK: weak internal PD (keep low at power-up)

License: GNU General Public License, version 2
Copyright © 2014-2018 Jared Boone
ShareBrained Technology, Inc.
Sheet: /hackrf_if/
File: hackrf_if.sch
Id: 4/6 Title: PortaPack H1

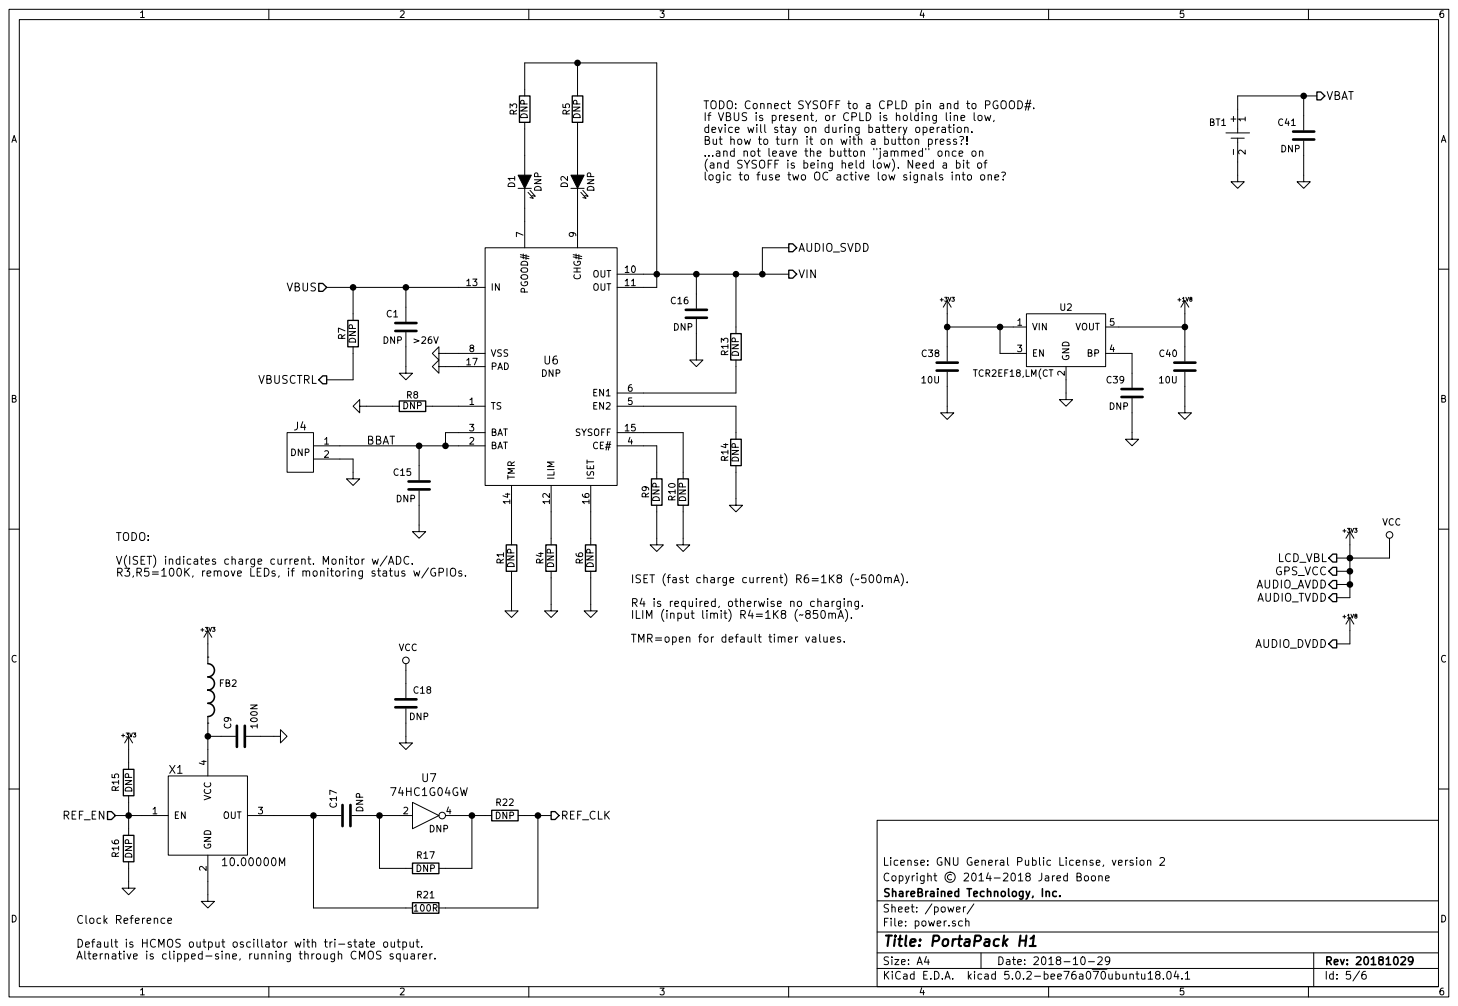
[picture p86: page 5]

TODO: Connect SYSOFF to a CPLD pin and to PGOOD#.
If VBUS is present, or CPLD is holding line low,
device will stay on during battery operation.
But how to turn it on with a button press?!
...and not leave the button "jammed" once on
(and SYSOFF is being held low). Need a bit of
logic to fuse two OC active low signals into one?

2 EN 3 BP 4 VOUT 5 U2 TCR2EF18,LM(CT C38

TODO:
V(ISET) indicates charge current. Monitor w/ADC.

R4 is required, otherwise no charging.
ILIM (input limit) R4=1K8 (850mA).

License: GNU General Public License, version 2
Copyright © 2014-2018 Jared Boone
ShareBrained Technology, Inc.
Sheet: /power/
File: power.sch
Id: 5/6 Title: PortaPack H1

Default is HCMOS output oscillator with tri-state output.

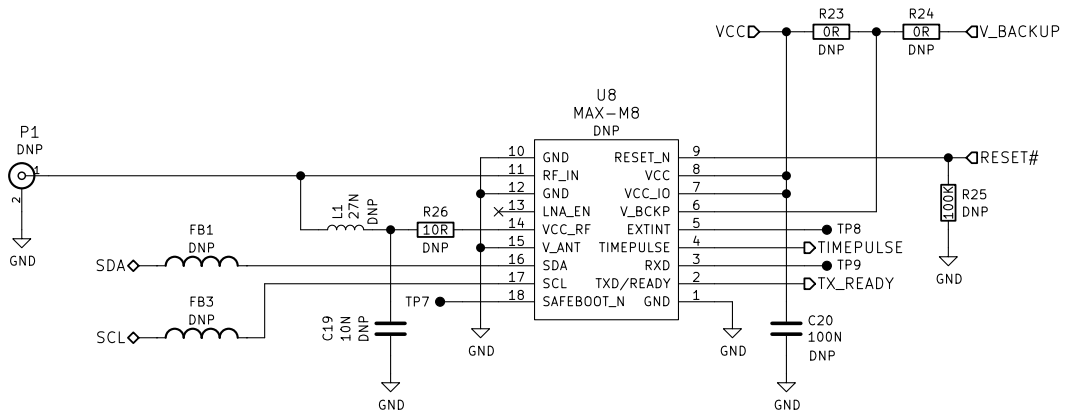
[picture p87: page 6]
