Josephrp/Meteor-On-Mesh/firmwares/mayhem-mdk/Source/main/sensordb.h

/*
 * Copyright (C) 2024 HTotoo
 *
 * This file is part of ESP32-Portapack.
 *
 * For additional license information, see the LICENSE file.
 */

#ifndef __SENSORDB_H__
#define __SENSORDB_H__

// This file is a DB for found I2C device addresses.
// SENSORS:
// - BH1750  - 0x23
// - HMC5883L  - 0x1E  - PARTLY
// - ADXL345 - 0x53  //https://github.com/craigpeacock/ESP32_Node/blob/master/main/adxl345.h
// - MPU925X ( 0x68 ) + 280  ( 0x76 )
// - LSM303  -  0x18 0x1e?!
// - SSD1306 - 0x3c 0x3d
// - SHT4X - 0x44

#include <inttypes.h>

typedef enum {
    BH1750 = 0,
    HMC5883L,
    ADXL345,
    MPU925X,
    BMx280,
    SHT3x,
    LSM303_ACCEL,
    LSM303_MAG,
    SSD1306,
    SHT4x,
    // Meshtonic H4M additional / muxed
    AS5600,
    BMI160,
    BMM150
} SENSORS;

#if __cplusplus
extern "C" {
#endif

void foundI2CDev(uint8_t addr);
void foundI2CDevOnChannel(uint8_t addr, uint8_t ch); // for muxed buses (H4M TCA)
uint8_t getDevAddr(SENSORS sensor);
uint8_t getSensorChannel(uint8_t addr); // 0-7 = TCA ch, 0xFE=direct, 0xFF=unknown

#if __cplusplus
}
#endif

#endif
